airtkey/onominer/pictures/IMG_20250701_171526.jpg

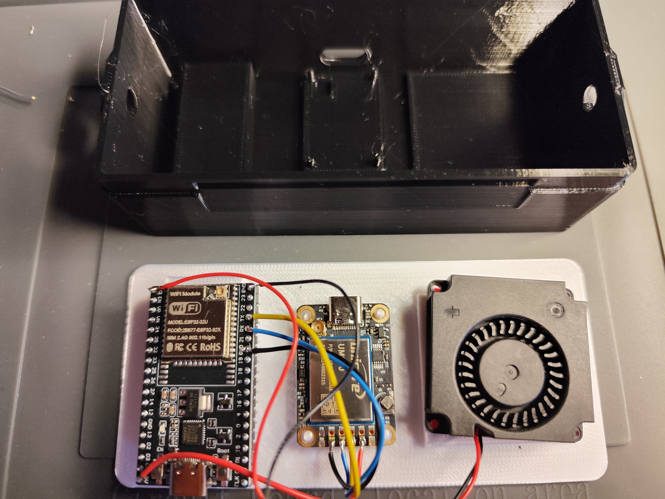
pictures/IMG_20250701_171526.jpg
